chill-avocado/radar-5g8-array/design/boards.png

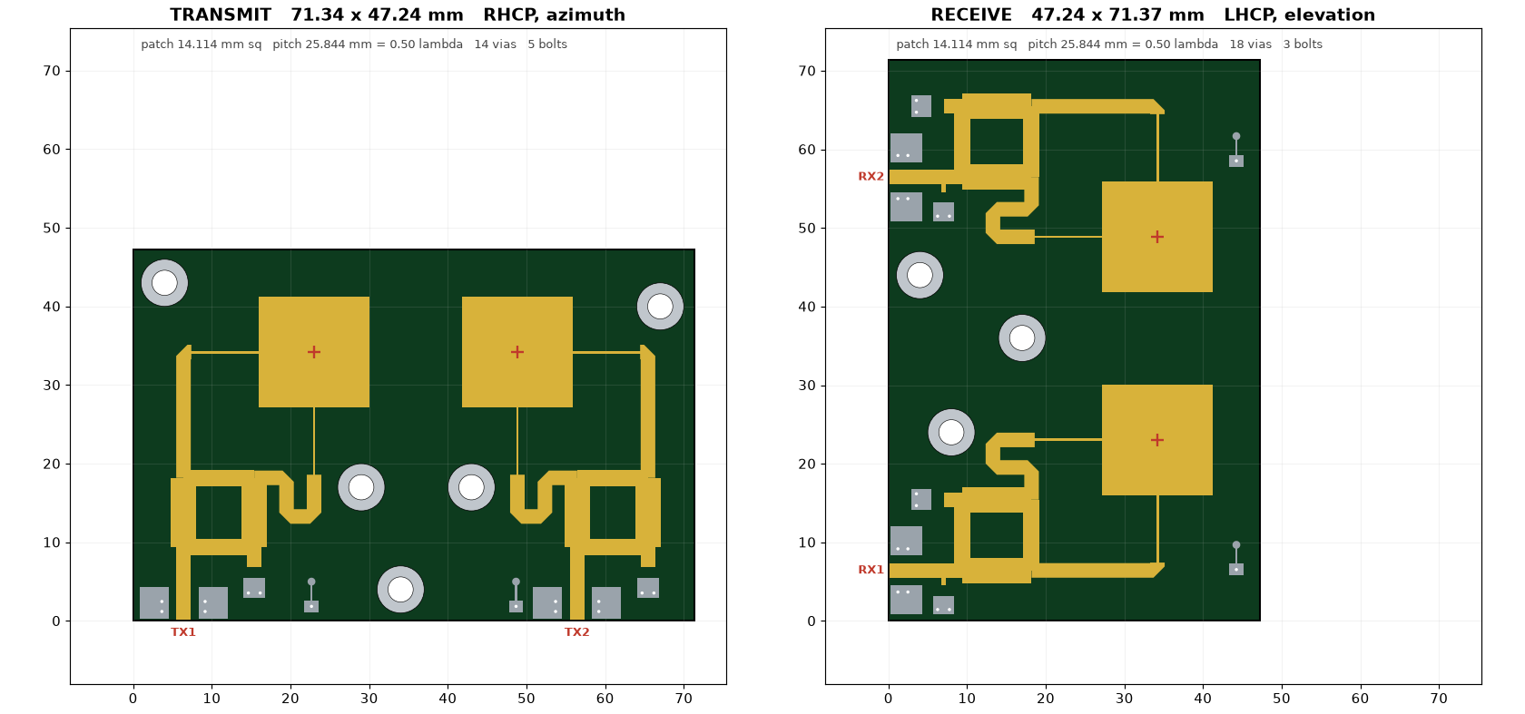
design/boards.png
