chill-avocado/radar-5g8-array/design/brd_lna.png

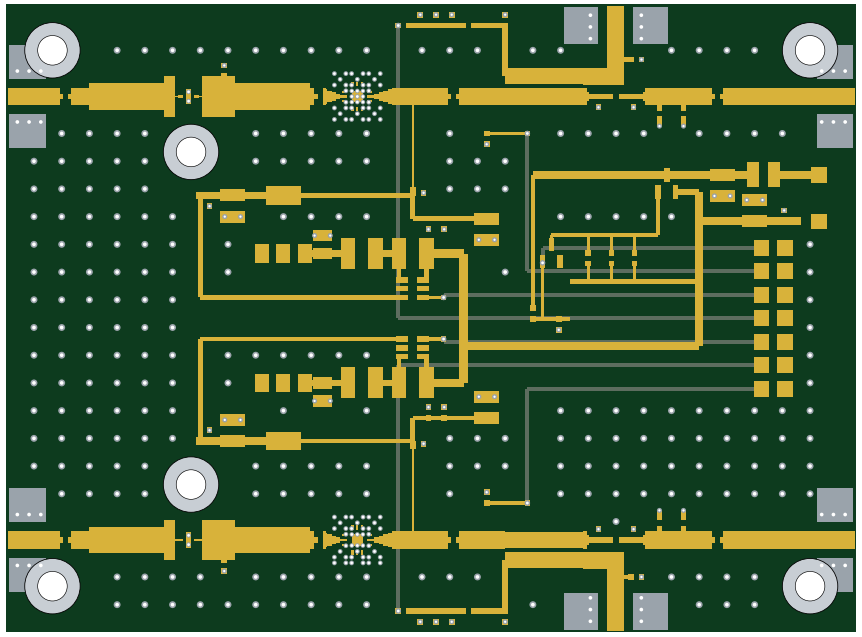
design/brd_lna.png
