chill-avocado/radar-5g8-array/design/brd_pa.png

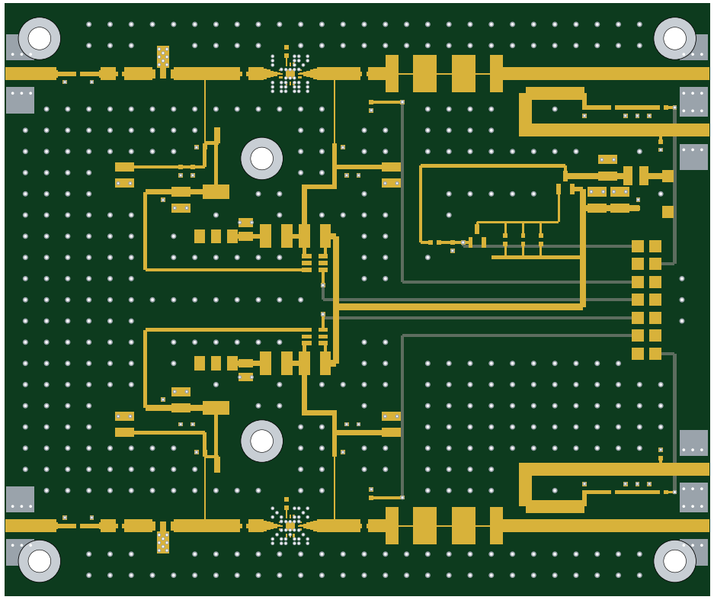
design/brd_pa.png
