chill-avocado/radar-5g8-array/design/brd_tx.png

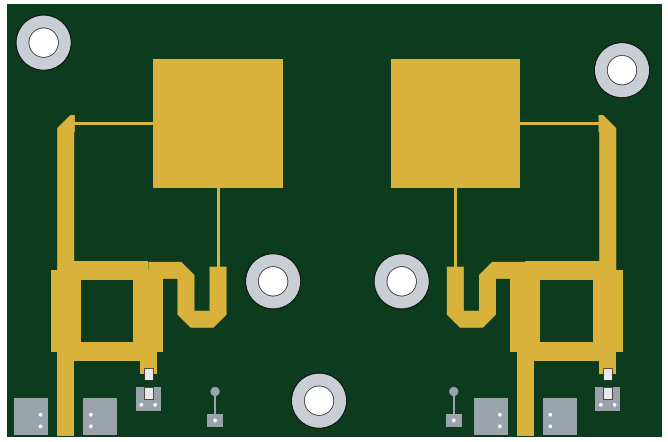
design/brd_tx.png
