chill-avocado/radar-5g8-array/design/element_compare.png

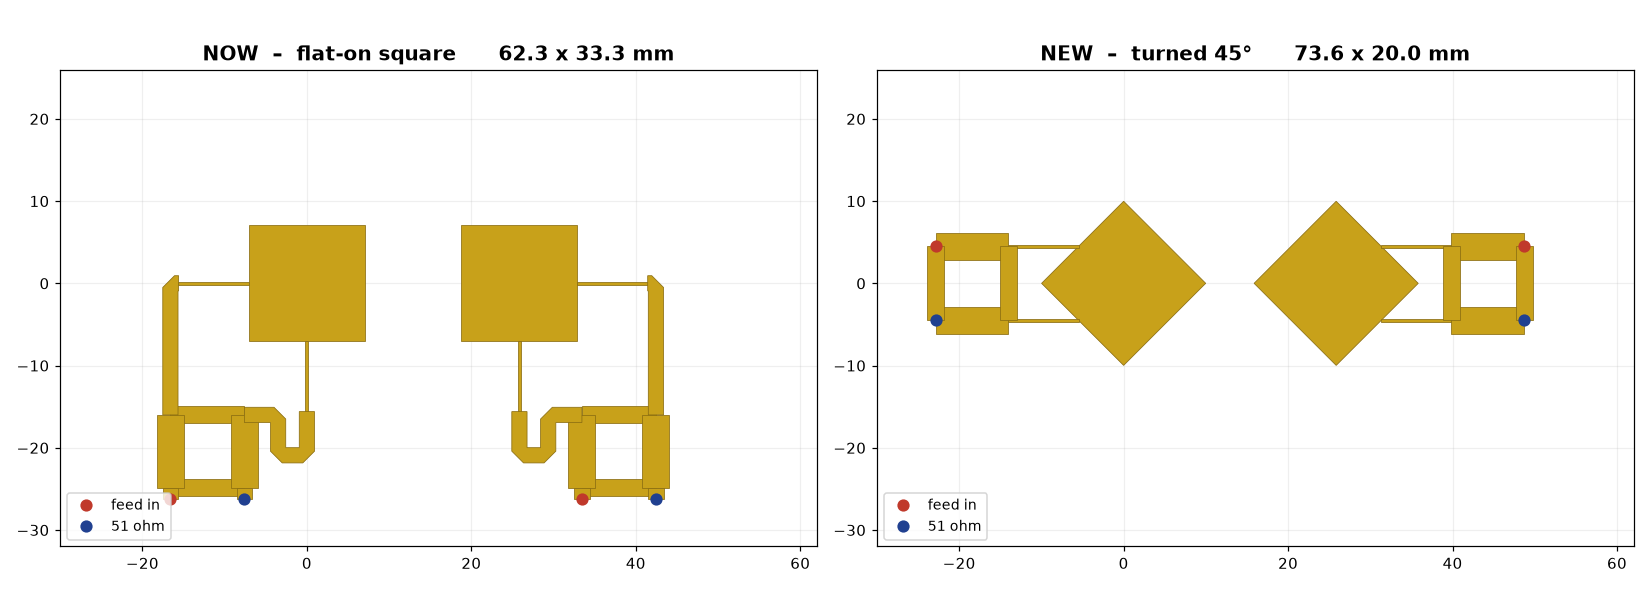
design/element_compare.png
