chill-avocado/radar-5g8-array/kicad/radar_5g8_receive_array/FAB_DRAWING_receive.png

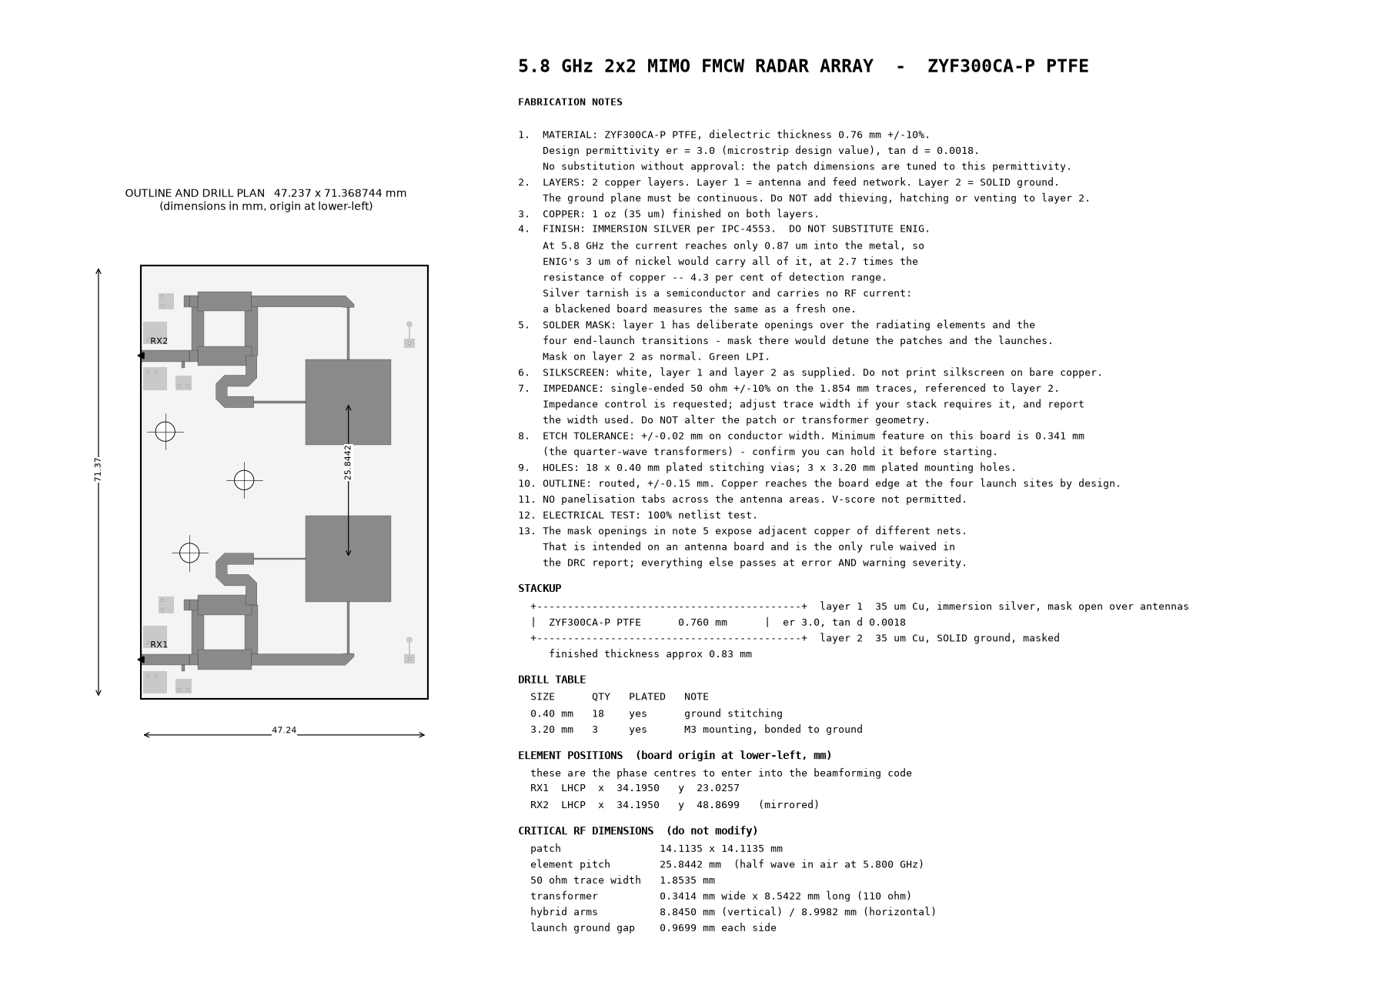
kicad/radar_5g8_receive_array/FAB_DRAWING_receive.png
