chill-avocado/radar-5g8-array/kicad/radar_5g8_receive_array/gerbers/gerber_check.png

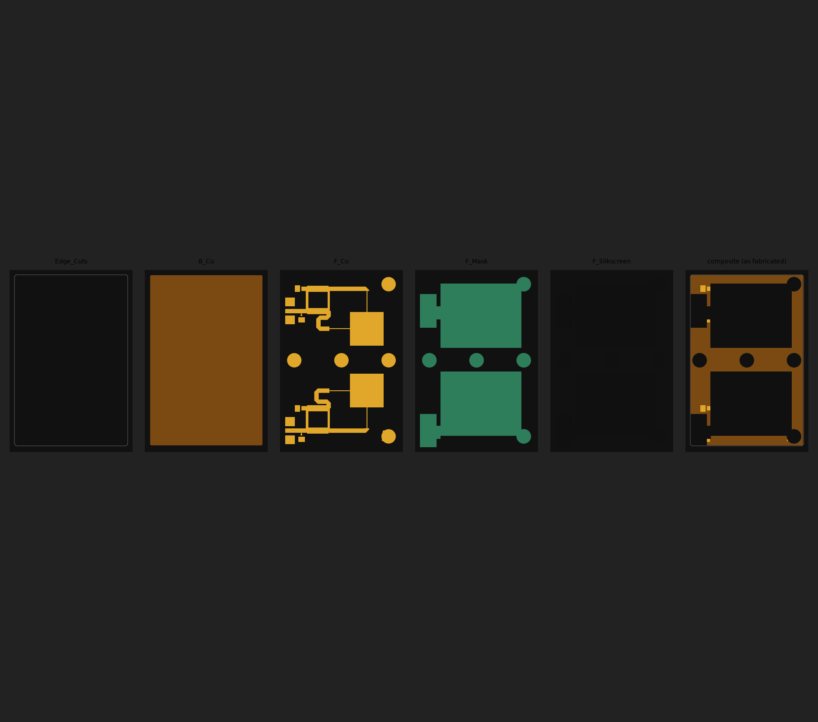
kicad/radar_5g8_receive_array/gerbers/gerber_check.png
