chill-avocado/radar-5g8-array/kicad/radar_5g8_transmit_array/FAB_DRAWING_transmit.png

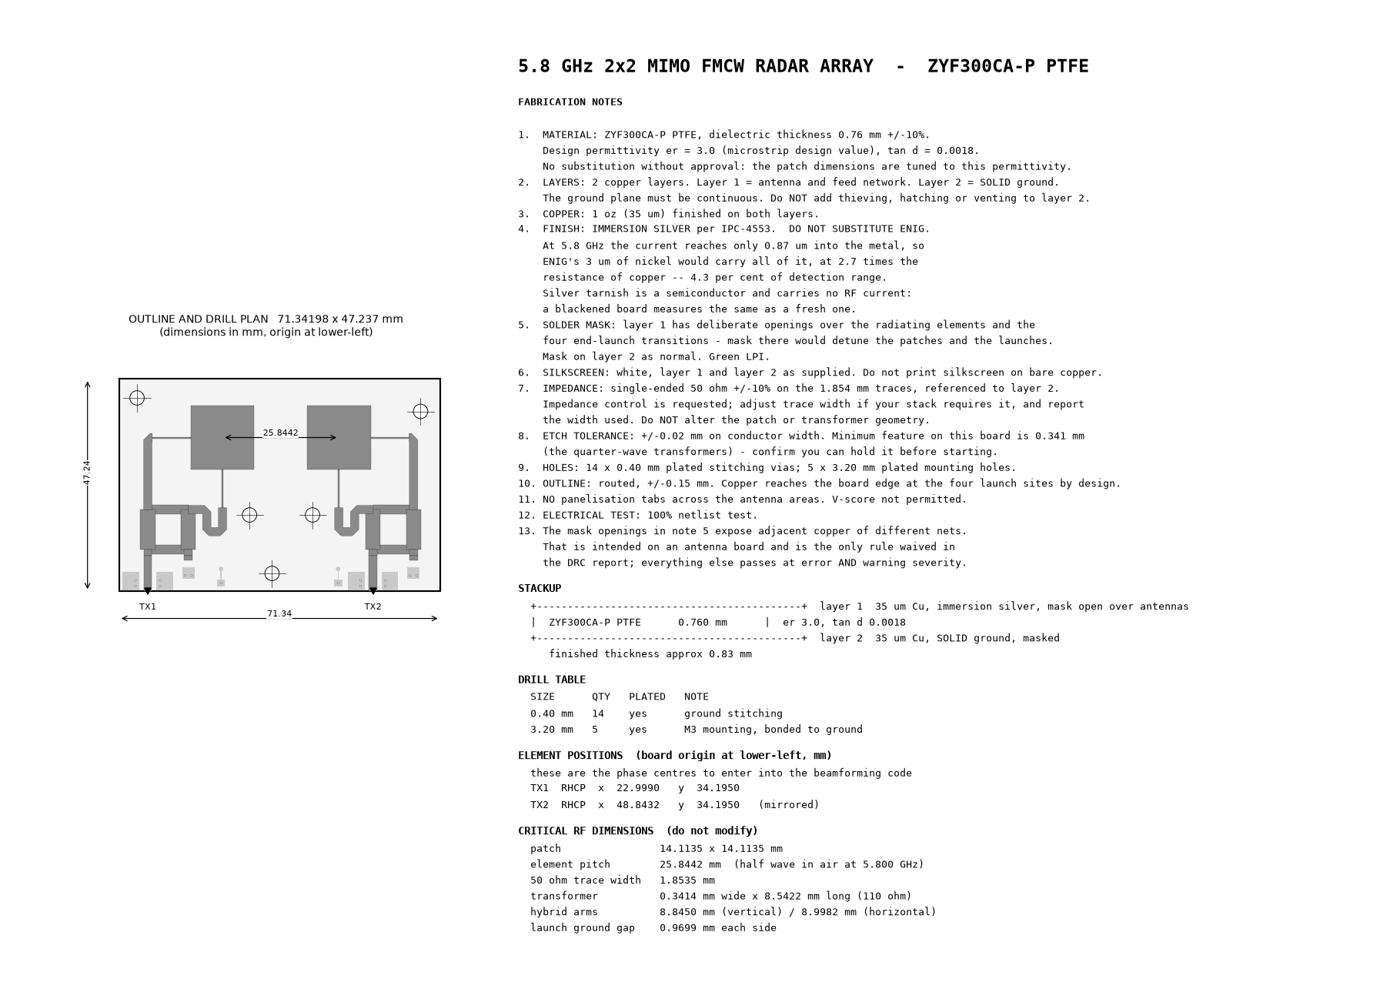
kicad/radar_5g8_transmit_array/FAB_DRAWING_transmit.png
