chill-avocado/radar-5g8-array/mech/back.png

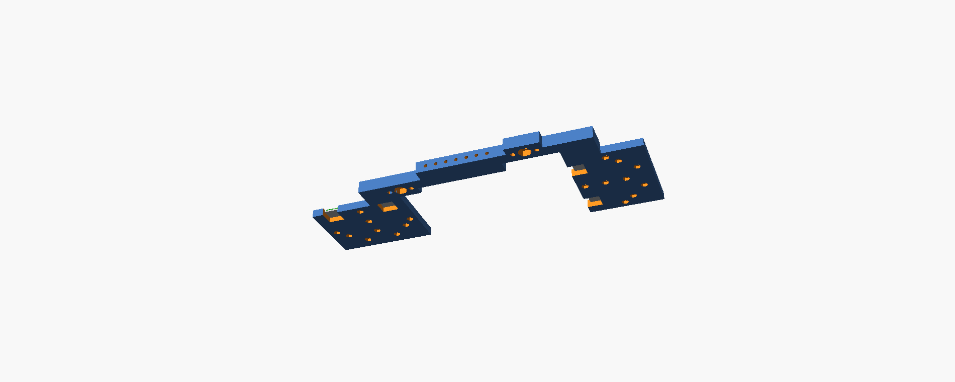
mech/back.png
