chill-avocado/radar-5g8-array/mech/half.png

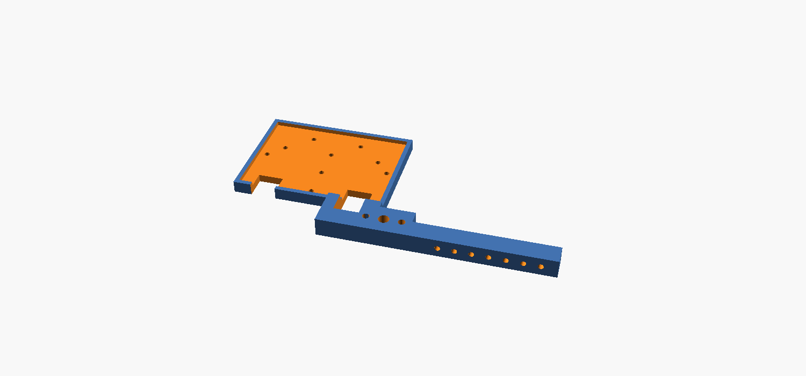
mech/half.png
