chill-avocado/radar-5g8-array/mech/metal.png

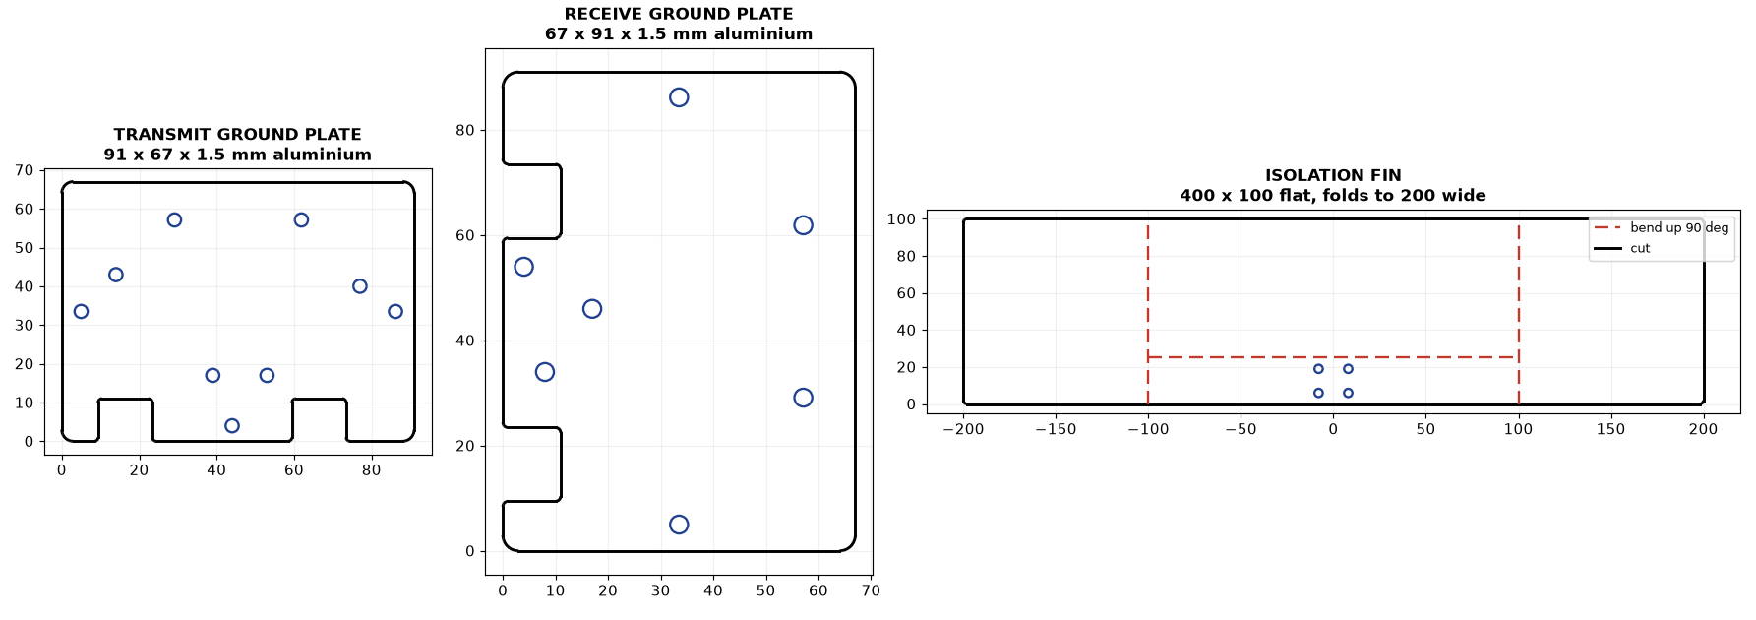
mech/metal.png
