chill-avocado/radar-5g8-array/mech/plates.png

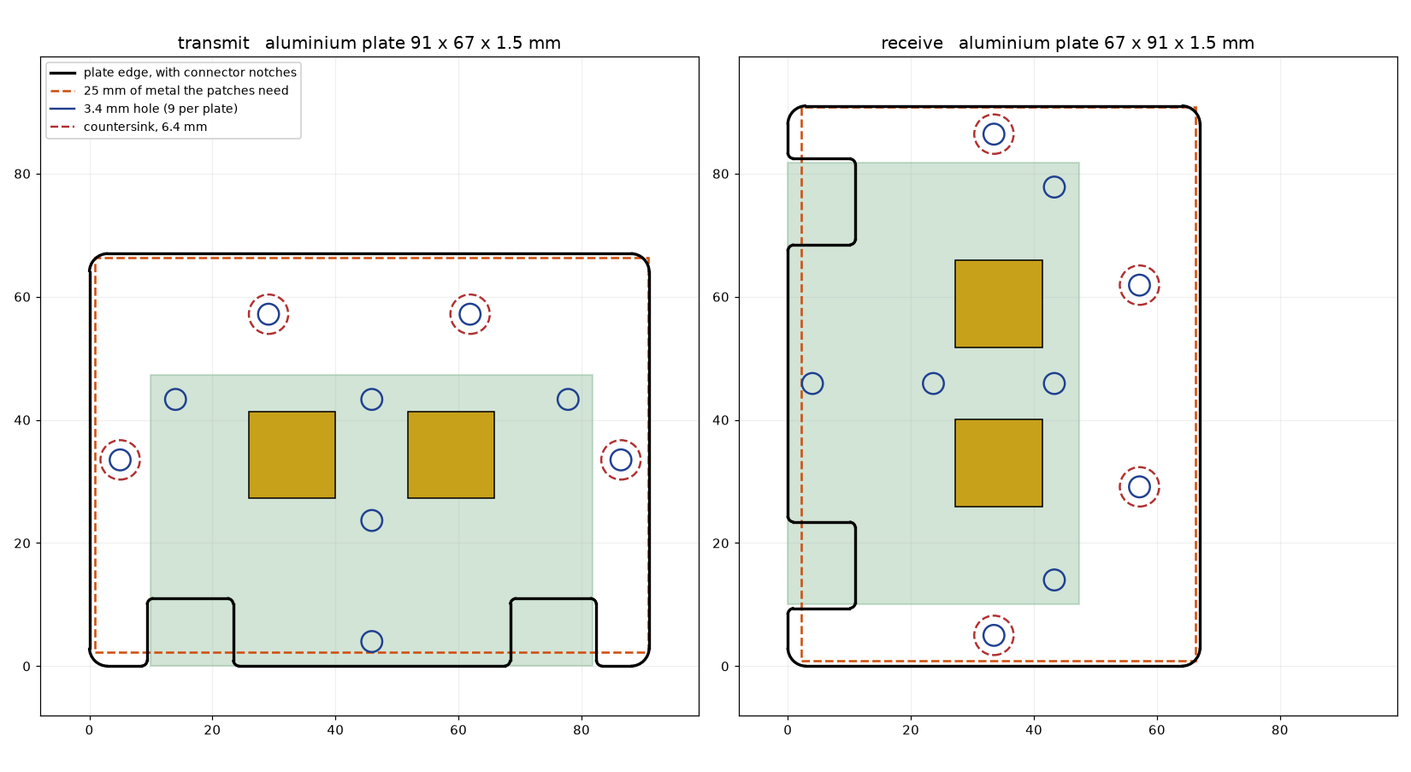
mech/plates.png
