chill-avocado/radar-5g8-array/mech/stack3d.png

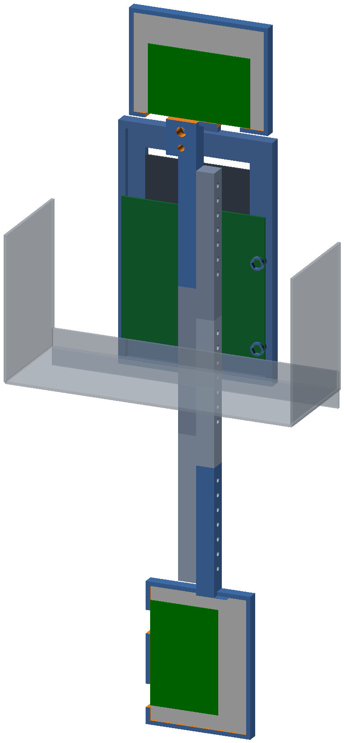
mech/stack3d.png
