chill-avocado/radar-5g8-array/mech/stack.png

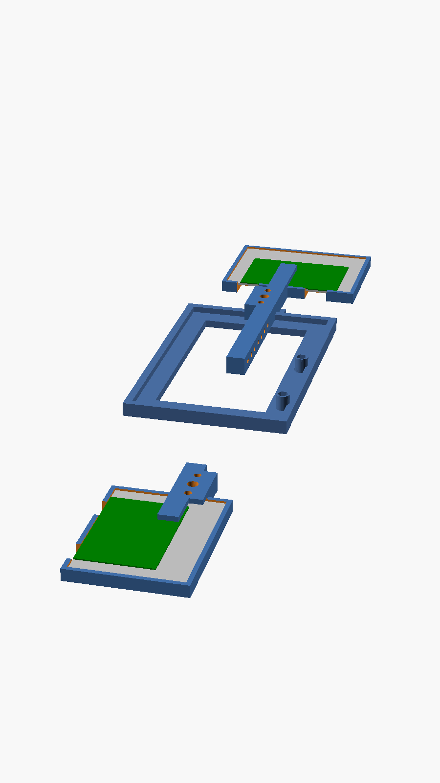
mech/stack.png
