chill-avocado/radar-5g8-array/SYSTEM.png

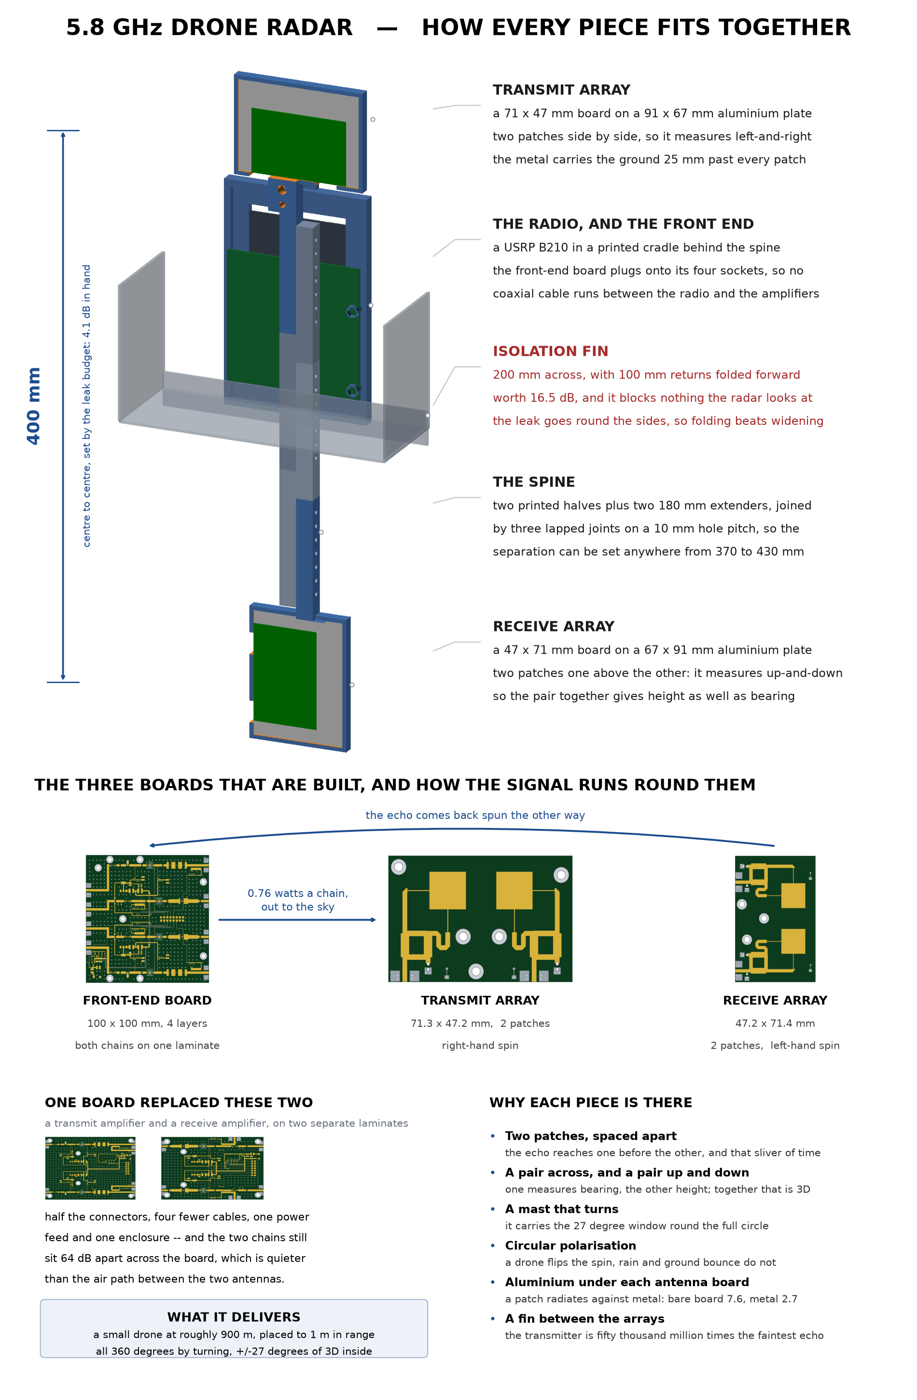
SYSTEM.png
