chill-avocado/radar-5g8-array/mech/assembly.png

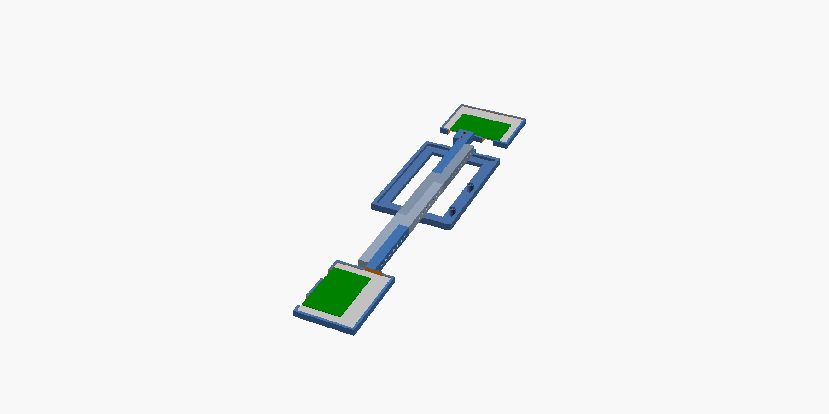
mech/assembly.png
