chill-avocado/radar-5g8-array/sim/results_fe8.png

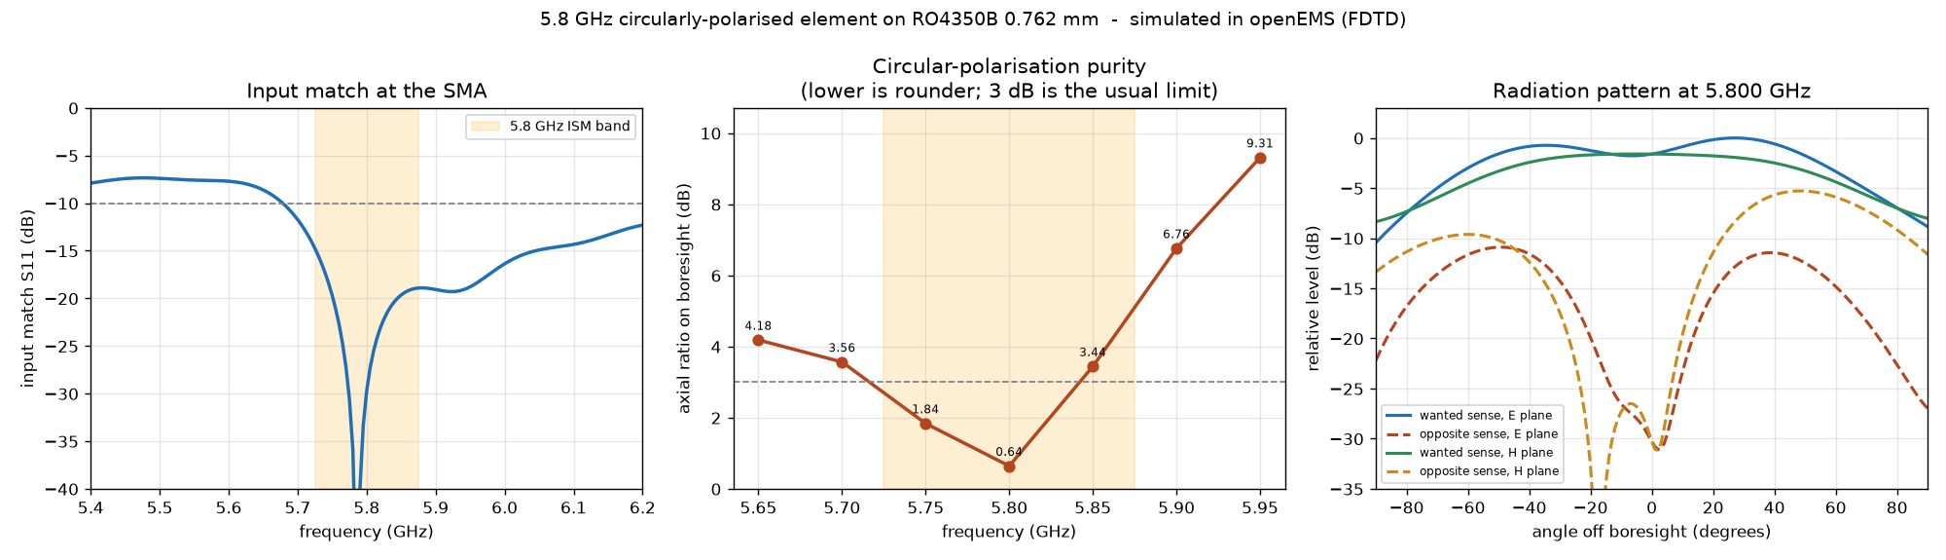
sim/results_fe8.png
