chill-avocado/radar-5g8-array/soft/src/track.cpp

//============================================================================
// track.cpp -- see track.hpp
//============================================================================
#include "radar/track.hpp"

#include <algorithm>
#include <cmath>

namespace radar {

namespace {

constexpr int NX = 6;   // state:       x y z vx vy vz
constexpr int NZ = 4;   // measurement: range, azimuth, elevation, range rate

inline double wrap_pi(double a) {
    while (a >  kPi) a -= 2.0 * kPi;
    while (a < -kPi) a += 2.0 * kPi;
    return a;
}

/// Cholesky inverse of a small real symmetric positive-definite matrix.
/// Returns false when the matrix is not positive definite, which for an
/// innovation covariance means the filter has diverged and the caller has to
/// refuse the update rather than propagate a nonsense gain.
bool sym_inverse4(const double A[NZ][NZ], double Ainv[NZ][NZ]) {
    double L[NZ][NZ] = {};
    for (int i = 0; i < NZ; ++i) {
        for (int j = 0; j <= i; ++j) {
            double sum = A[i][j];
            for (int k = 0; k < j; ++k) sum -= L[i][k] * L[j][k];
            if (i == j) {
                if (!(sum > 0.0) || !std::isfinite(sum)) return false;
                L[i][i] = std::sqrt(sum);
            } else {
                L[i][j] = sum / L[j][j];
            }
        }
    }
    double Li[NZ][NZ] = {};
    for (int c = 0; c < NZ; ++c) {
        Li[c][c] = 1.0 / L[c][c];
        for (int r = c + 1; r < NZ; ++r) {
            double sum = 0.0;
            for (int k = c; k < r; ++k) sum += L[r][k] * Li[k][c];
            Li[r][c] = -sum / L[r][r];
        }
    }
    for (int i = 0; i < NZ; ++i)
        for (int j = 0; j < NZ; ++j) {
            double sum = 0.0;
            for (int k = std::max(i, j); k < NZ; ++k) sum += Li[k][i] * Li[k][j];
            Ainv[i][j] = sum;
        }
    return true;
}

} // namespace

//============================================================================
Scales resolution_scales(const Config& cfg) {
    Scales s;
    s.lambda_m = (cfg.d.lambda_m > 0)
                     ? cfg.d.lambda_m
                     : phys::c0 / (cfg.centre_freq_hz > 0 ? cfg.centre_freq_hz
                                                          : array_geom::f0_hz);

    // Range resolution is set by the swept bandwidth alone: two echoes are
    // separable when their round-trip delay differs by more than one over the
    // bandwidth.  Zero padding the transform makes the bins finer than this
    // but does not make the radar see any more detail, which is exactly why
    // the measurement noise has to come from the resolution and not the bin.
    s.range_res_m = (cfg.d.range_res_m > 0) ? cfg.d.range_res_m
                                            : phys::c0 / (2.0 * std::max(1.0, cfg.sweep_bw_hz));

    const double t_pri = (cfg.d.t_pri_s > 0)
                             ? cfg.d.t_pri_s
                             : double(cfg.n_pri) / std::max(1.0, cfg.sample_rate_hz);
    // In time-division multiplexing the two transmitters take turns, so a
    // given virtual channel is only refreshed every other pulse repetition
    // interval.  Its slow-time sample rate, and therefore the unambiguous
    // velocity, is halved.
    const int    tdm_factor = (cfg.mimo == MimoMode::Tdm) ? array_geom::n_tx : 1;
    const double t_slow     = t_pri * tdm_factor;

    s.t_cpi_s     = (cfg.d.t_cpi_s > 0) ? cfg.d.t_cpi_s : t_slow * cfg.n_chirp;
    s.prf_slow_hz = (t_slow > 0) ? 1.0 / t_slow : 0.0;
    s.vel_res_ms  = (cfg.d.vel_res_ms > 0) ? cfg.d.vel_res_ms
                                           : s.lambda_m / (2.0 * std::max(1e-9, s.t_cpi_s));
    s.vel_max_ms  = (cfg.d.vel_max_ms > 0) ? cfg.d.vel_max_ms
                                           : s.lambda_m * s.prf_slow_hz / 4.0;
    return s;
}

//============================================================================
Tracker::Tracker(const Config& cfg)
    : cfg_(cfg),
      sc_(resolution_scales(cfg)),
      q_accel_(cfg.track_q_accel > 0 ? cfg.track_q_accel : 1.0),
      gate_(cfg.track_gate_chi2 > 0 ? cfg.track_gate_chi2 : 16.0),
      confirm_n_(std::max(1, cfg.track_confirm_n)),
      drop_n_(std::max(1, cfg.track_drop_n)) {

    // A bin index is a quantised measurement, and a quantised measurement is
    // uniformly distributed inside its bin.  The standard deviation of a
    // uniform distribution one bin wide is that width over the square root of
    // twelve; there is nothing to tune here.
    sigma_r_  = sc_.range_res_m / std::sqrt(12.0);
    sigma_rr_ = sc_.vel_res_ms  / std::sqrt(12.0);

    // Angle precision comes from phase, so the constant that matters is how
    // many radians of phase one unit of direction cosine buys.  That is the
    // wavenumber times the aperture, taken from the element positions rather
    // than assumed, so a retuned carrier or a different board changes it
    // automatically.
    double xmin = 1e30, xmax = -1e30, ymin = 1e30, ymax = -1e30;
    for (int i = 0; i < array_geom::n_virt; ++i) {
        xmin = std::min(xmin, array_geom::virt_xy[i][0]);
        xmax = std::max(xmax, array_geom::virt_xy[i][0]);
        ymin = std::min(ymin, array_geom::virt_xy[i][1]);
        ymax = std::max(ymax, array_geom::virt_xy[i][1]);
    }
    const double k0 = 2.0 * kPi / sc_.lambda_m;
    k_phase_x_ = k0 * std::max(1e-9, xmax - xmin);
    k_phase_y_ = k0 * std::max(1e-9, ymax - ymin);

    // Half-power width of the array pattern along each axis, measured from the
    // same element positions.  Two elements spaced half a wavelength give a
    // pattern that falls to half power at a direction cosine of one half, so
    // this comes out at sixty degrees -- a very wide beam, which is why the
    // angle accuracy has to be bought with signal-to-noise ratio.
    auto pattern = [&](double u, double v) {
        double re = 0, im = 0;
        for (int i = 0; i < array_geom::n_virt; ++i) {
            const double p = k0 * (array_geom::virt_xy[i][0] * u + array_geom::virt_xy[i][1] * v);
            re += std::cos(p); im += std::sin(p);
        }
        return re * re + im * im;
    };
    auto hpbw = [&](bool along_x) {
        const double p0 = pattern(0, 0);
        double prev = p0, prev_a = 0.0;
        for (int i = 1; i <= 9000; ++i) {
            const double a = rad(i * 0.01);
            const double p = along_x ? pattern(std::sin(a), 0.0) : pattern(0.0, std::sin(a));
            if (p <= 0.5 * p0) {
                const double f = (prev - 0.5 * p0) / (prev - p);
                return 2.0 * deg(prev_a + f * (rad(i * 0.01) - prev_a));
            }
            prev = p; prev_a = a;
        }
        return 180.0;
    };
    bw_az_deg_ = hpbw(true);
    bw_el_deg_ = hpbw(false);

    // No array is calibrated better than a fraction of a degree, so however
    // strong the echo the angle error never goes below this.  A filter that
    // believes an infinitely precise measurement stops listening to its own
    // model and starts chasing every fluctuation.
    sigma_ang_floor_ = rad(0.2);

    tracks_.reserve(64);
    pairs_.reserve(256);
}

void Tracker::reset() {
    tracks_.clear();
    next_id_ = 1;
}

std::size_t Tracker::n_confirmed() const {
    std::size_t k = 0;
    for (const Track& t : tracks_) if (t.confirmed) ++k;
    return k;
}
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
